lhkhanh080720/HCMUT_The_Fire_Detection/Code Py Win/MulticamWindow.py

from libs import *

# Real Camera
camera_id = "/dev/video1"
videoCapture = cv2.VideoCapture(camera_id, cv2.CAP_V4L2)
# Zoom Camera
camID = 'nvarguscamerasrc ! video/x-raw(memory:NVMM), width=640, height=480, format=NV12, framerate=21/1 ! nvvidconv flip-method='+'2'+' ! video/x-raw, width='+'640'+', height='+'480'+', format=BGRx ! videoconvert ! video/x-raw, format=BGR ! appsink' 
cam = cv2.VideoCapture(camID)
# Wait a second to let the port initialize
time.sleep(1)

class MultiCamera:
    numClass = 2     #The numbers of classes
    cls_dict = get_cls_dict(numClass)
    vis = BBoxVisualization(cls_dict)
    trt_yolo = TrtYOLO('obj', numClass, False)

    def __init__(self, para_source) -> None:
        self.source = para_source
        self.frame = None
    
    def getFrame(self, nameCam=str):
        # The method for using OpenCV grab() - retrieve()
        # We are not using read() here because, documentation insists that it is slower in multi-thread environment.
        # capture.grab()
        # ret, frame = capture.retrieve()
        para_source = self.source
        para_source.grab()

        ret, frame = para_source.retrieve()
        #===Detect The Fire===
        self.detectObjects(MultiCamera.trt_yolo, MultiCamera.vis, frame)

        if not ret:
            print("empty frame")
            return
        self.frame = frame
        cv2.imshow(nameCam, self.frame)

    def detectObjects(self, trt_yolo, vis, frame):   
        boxes, confs, clss = trt_yolo.detect(frame, 0.3)

        #Precise poison filter (> 0.6)
        indexDel = []
        for index, value in enumerate(confs):
            if value <= 0.7:
                indexDel.append(index)
        boxes = np.delete(boxes, indexDel, 0)
        confs = np.delete(confs, indexDel)
        clss = np.delete(clss, indexDel)
        
        if len(confs) > 0: 
            self.frame, (x_min, y_min, x_max, y_max) = vis.draw_bboxes(frame, boxes, confs, clss)

# 2 object in class MultiCamera
realCam = MultiCamera(videoCapture)
zoomCam = MultiCamera(cam)
while True:
    realCam.getFrame("realCam")
    cv2.moveWindow("realCam", 0, 0)

    zoomCam.getFrame("zoomCam")
    cv2.moveWindow("zoomCam", 650, 0)

    if cv2.waitKey(1) == ord('q'): #check Button 'q' in 1 milis and do st...
        break
videoCapture.release()
cam.release()
cv2.destroyAllWindows()
