lhkhanh080720/HCMUT_The_Fire_Detection/Code Py Win/Code Drive/tensorrt_demos/libs.py

from PyQt5 import QtCore, QtGui, QtWidgets
from GUI.ui_interface import Ui_MainWindow
from PyQt5.QtWidgets import QApplication, QMainWindow, QLabel
from PyQt5.QtGui import QImage, QPixmap
import sys
import cv2
import numpy as np
import threading
import time
import psutil
import datetime

import cv2
import pycuda.autoinit  # This is needed for initializing CUDA driver

from utils.yolo_classes import get_cls_dict
from utils.visualization import BBoxVisualization
from utils.yolo_with_plugins import TrtYOLO
